jyuenger/Tierwriter/Miscellaneous/Renders/03.png

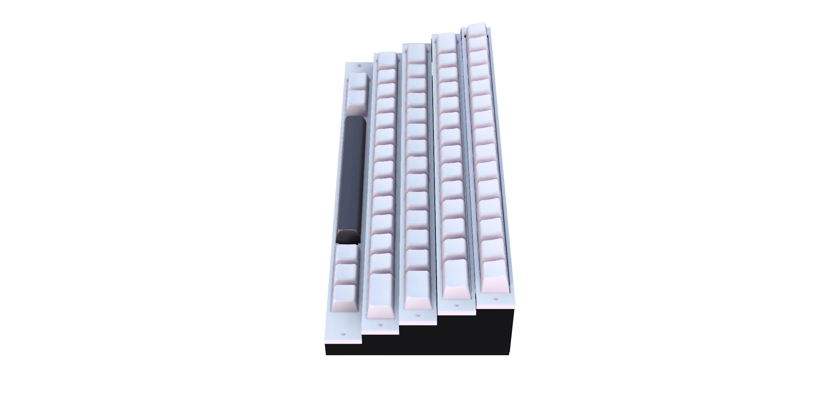
Miscellaneous/Renders/03.png
