jyuenger/Tierwriter/Miscellaneous/Renders/04.png

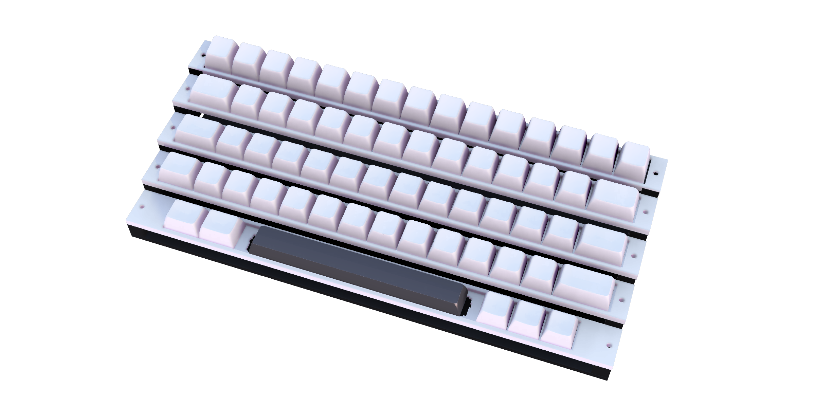
Miscellaneous/Renders/04.png
