jyuenger/Tierwriter/Miscellaneous/Renders/06.png

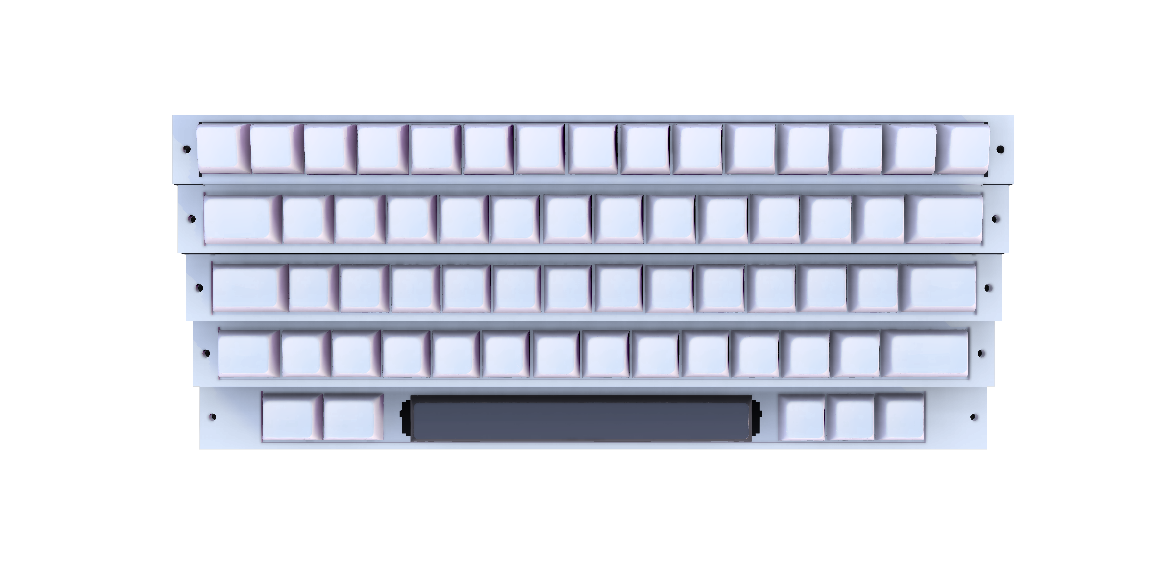
Miscellaneous/Renders/06.png
